serenebliss0/esp32-smart-speaker/webpage-screenshots/Screenshot 2026-03-15 223149.png

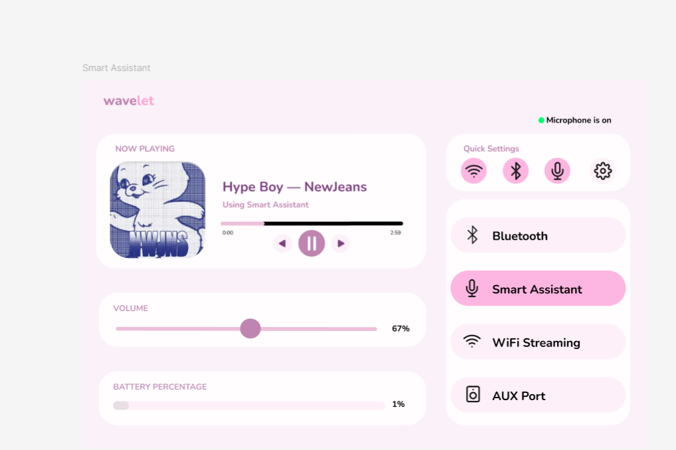
webpage-screenshots/Screenshot 2026-03-15 223149.png
