serenebliss0/esp32-smart-speaker/webpage-screenshots/Screenshot 2026-03-17 110921.png

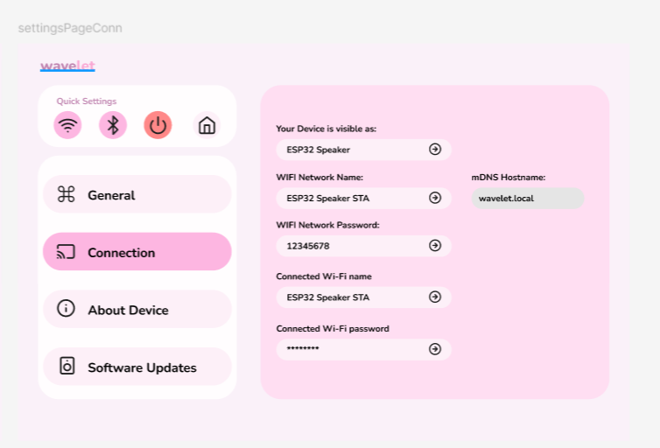
webpage-screenshots/Screenshot 2026-03-17 110921.png
